LincolnProenca/redragon-cobra-zmk-mod/PCB/Rev2/IMG_20260424_192445.jpg

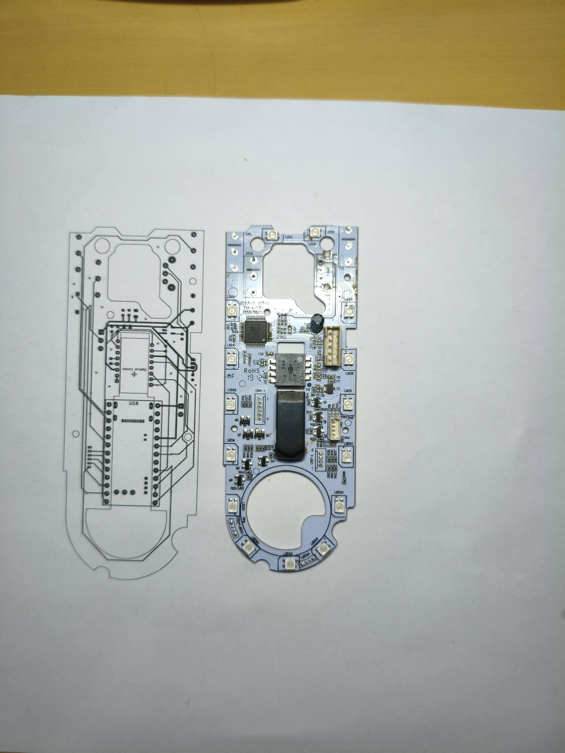
PCB/Rev2/IMG_20260424_192445.jpg
