LincolnProenca/redragon-cobra-zmk-mod/PCB/Rev2/MVIMG_20260422_195017.jpg

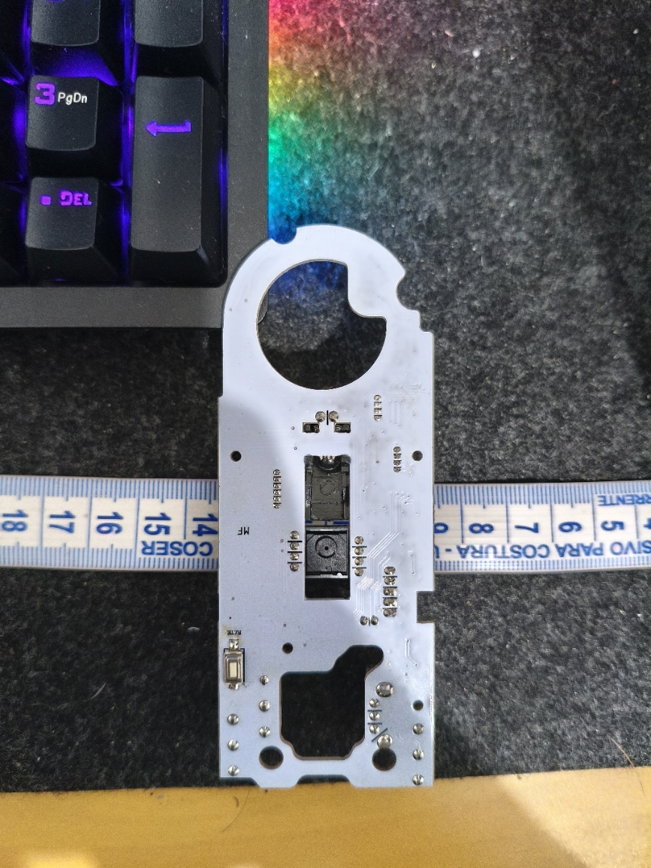
PCB/Rev2/MVIMG_20260422_195017.jpg
