LincolnProenca/redragon-cobra-zmk-mod/PCB/Rev2/MVIMG_20260429_194614.jpg

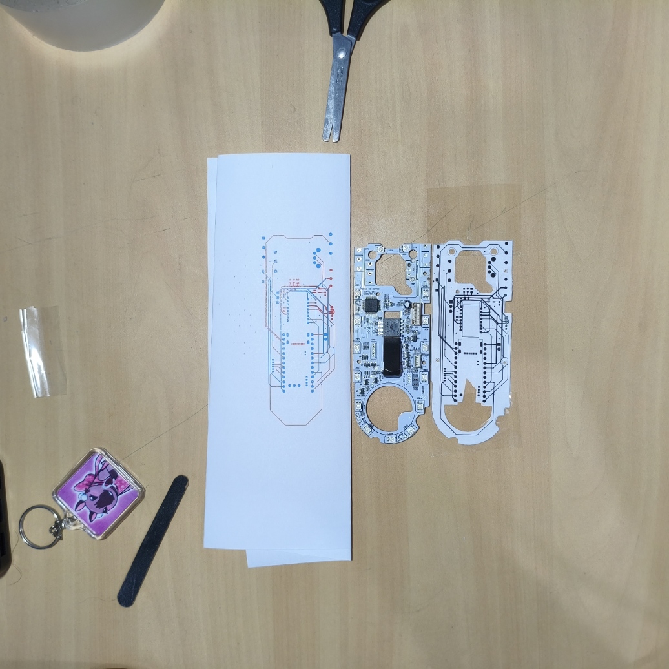
PCB/Rev2/MVIMG_20260429_194614.jpg
