LincolnProenca/redragon-cobra-zmk-mod/PCB/Rev2/reference5.png

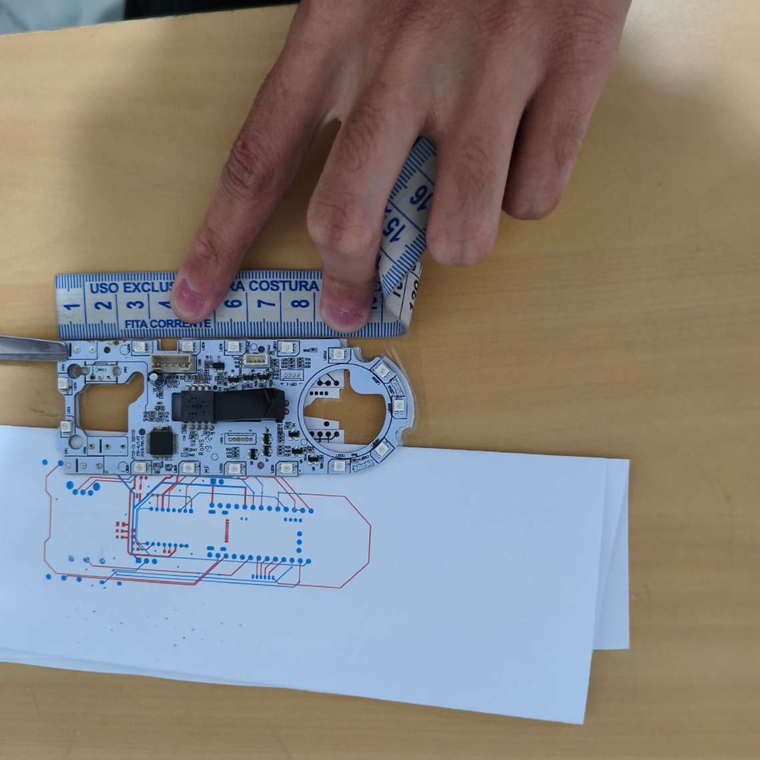
PCB/Rev2/reference5.png
