LincolnProenca/redragon-cobra-zmk-mod/PCB/Rev2/reference.png

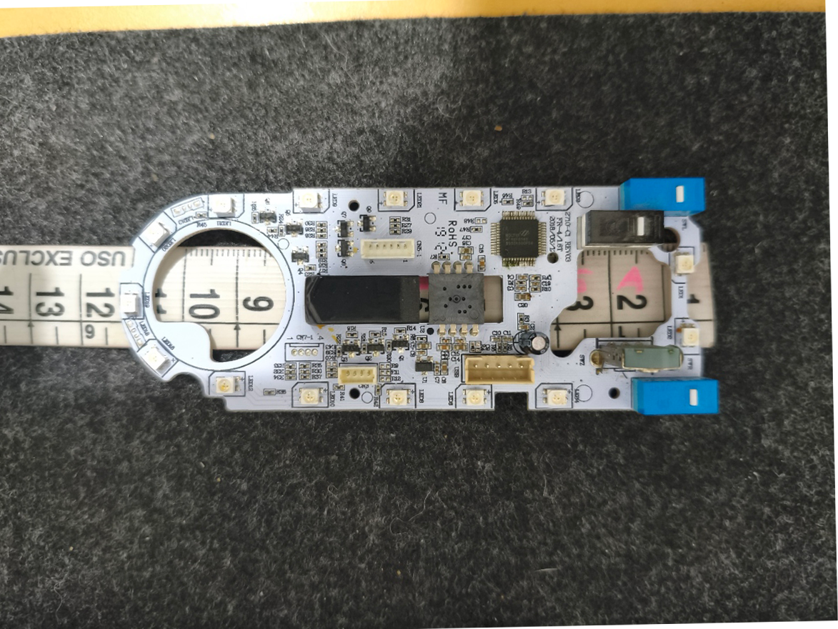
PCB/Rev2/reference.png
